OmarSall/Portfolio/Harvester Prototype/Gauder_magnet_case_assembly.SLDASM

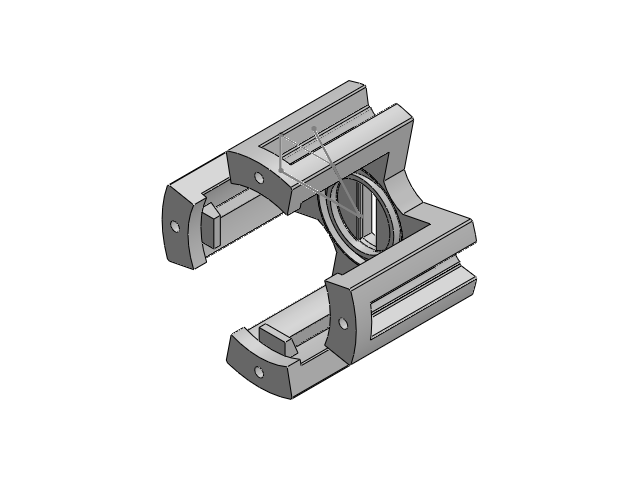
[picture p52: CAD file, 2026-01-31]
Harvester Prototype/Gauder_magnet_case_assembly.SLDASM
N_carc_sup
N_tapa_carc_sup
