OmarSall/Portfolio/Harvester Prototype/Gauder_assempby_separate.SLDASM

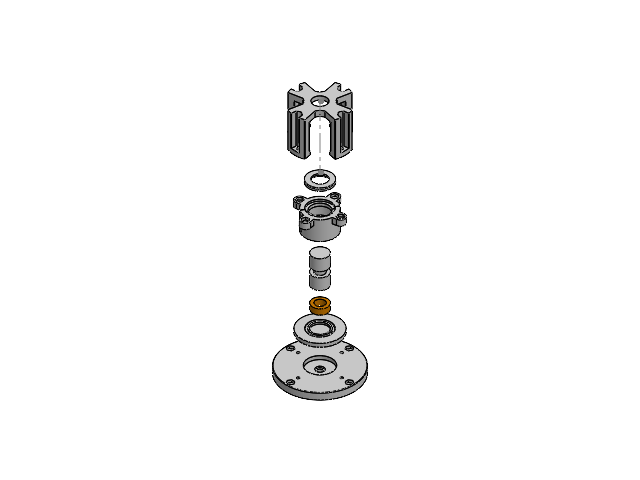
[picture p53: CAD file, 2026-01-31]
Harvester Prototype/Gauder_assempby_separate.SLDASM
p1p_Carc_inf
p1p_O1_Base
p1p_N_carc_sup
coil_case_OD35
p1p_N_tapa_carc_sup
coil_1c_OD35
p1p_magnetcase_dr
p1p_magnetcase_esq
